mabeckgit/pi-microscope/Drawings/camera_module/OTHER_FORMATS/RspCameraMia/plastic_Smooth_bump.png

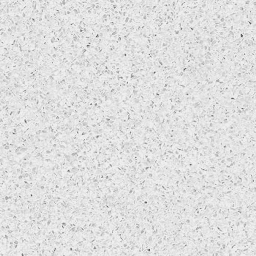
Drawings/camera_module/OTHER_FORMATS/RspCameraMia/plastic_Smooth_bump.png
