mabeckgit/pi-microscope/Drawings/camera_module/RENDERS/PiCamera2back.png

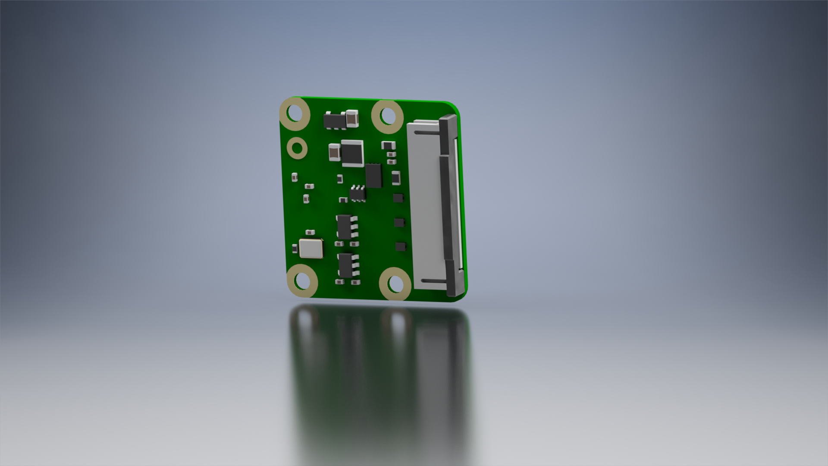
Drawings/camera_module/RENDERS/PiCamera2back.png
