mabeckgit/pi-microscope/Drawings/camera_module/RENDERS/PiCamera2front.png

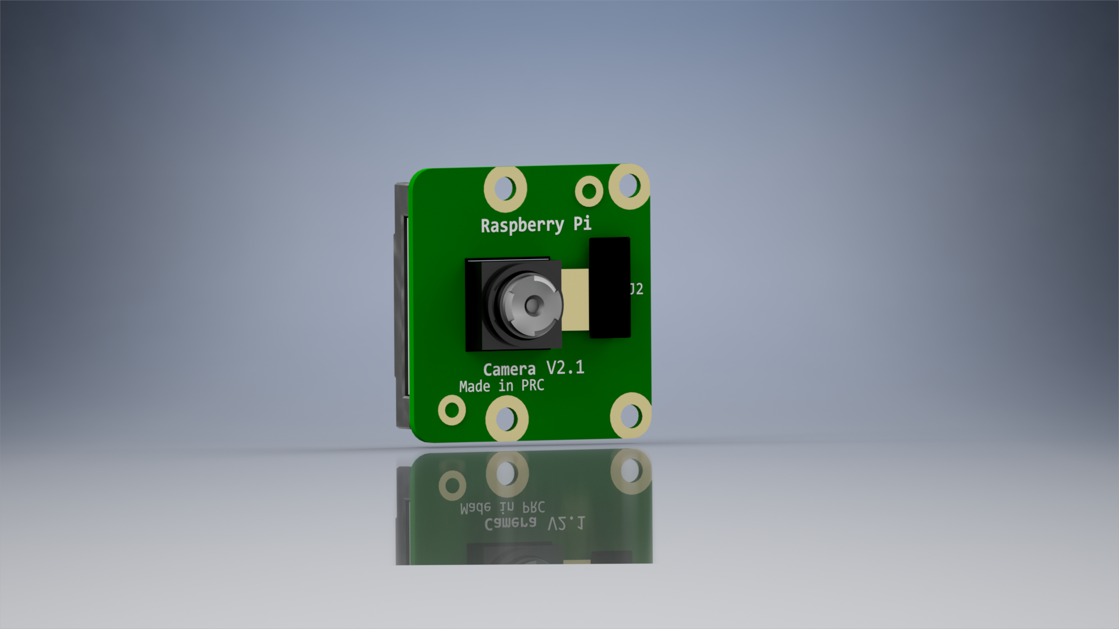
Drawings/camera_module/RENDERS/PiCamera2front.png
