mabeckgit/pi-microscope/Drawings/camera_module/RENDERS/PiCamera2side.png

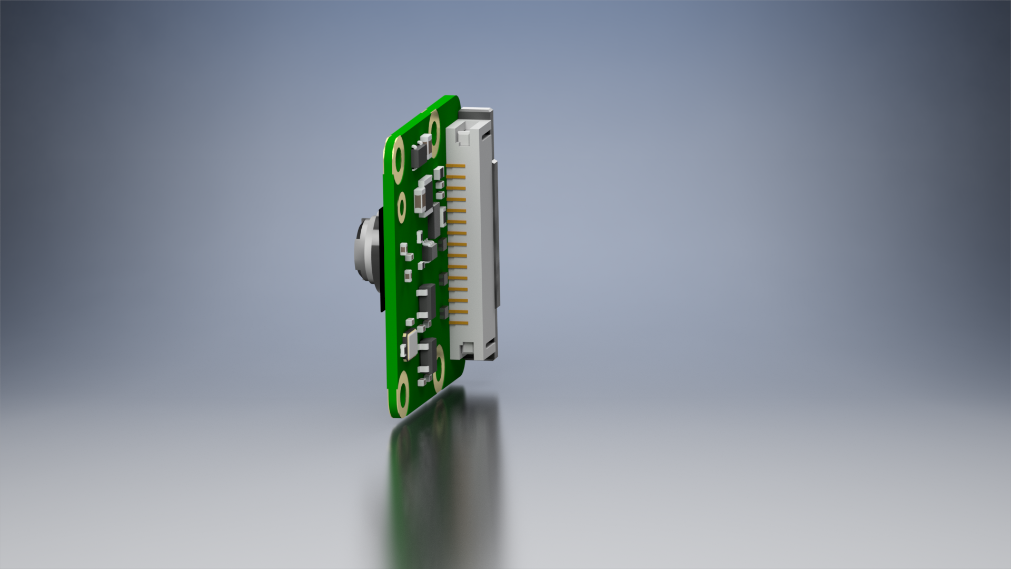
Drawings/camera_module/RENDERS/PiCamera2side.png
