mabeckgit/pi-microscope/Program/1.jpg

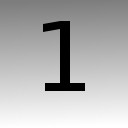
Program/1.jpg
