mabeckgit/pi-microscope/Program/2.jpg

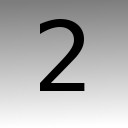
Program/2.jpg
