mabeckgit/pi-microscope/Program/3.jpg

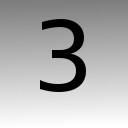
Program/3.jpg
