mabeckgit/pi-microscope/Program/wxGlade-1.0.1/wxGlade-1.0.1/docs/html/_images/Calculator06_P0P0.png

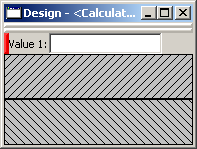
Program/wxGlade-1.0.1/wxGlade-1.0.1/docs/html/_images/Calculator06_P0P0.png
