mabeckgit/pi-microscope/Program/wxGlade-1.0.1/wxGlade-1.0.1/docs/html/_images/Calculator06_P1P0.png

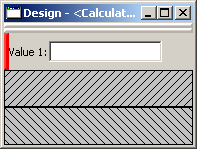
Program/wxGlade-1.0.1/wxGlade-1.0.1/docs/html/_images/Calculator06_P1P0.png
