mabeckgit/pi-microscope/Program/wxGlade-1.0.1/wxGlade-1.0.1/docs/html/_images/Calculator07_Menu_Editor.png

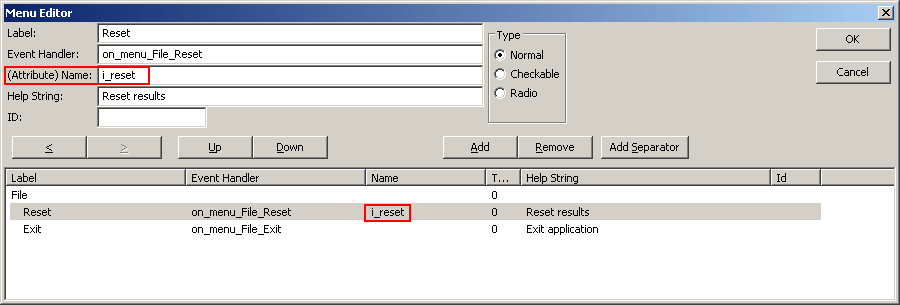
Program/wxGlade-1.0.1/wxGlade-1.0.1/docs/html/_images/Calculator07_Menu_Editor.png
