mabeckgit/pi-microscope/Program/wxGlade-1.0.1/wxGlade-1.0.1/docs/html/_images/Calculator_06_PythonCode.png

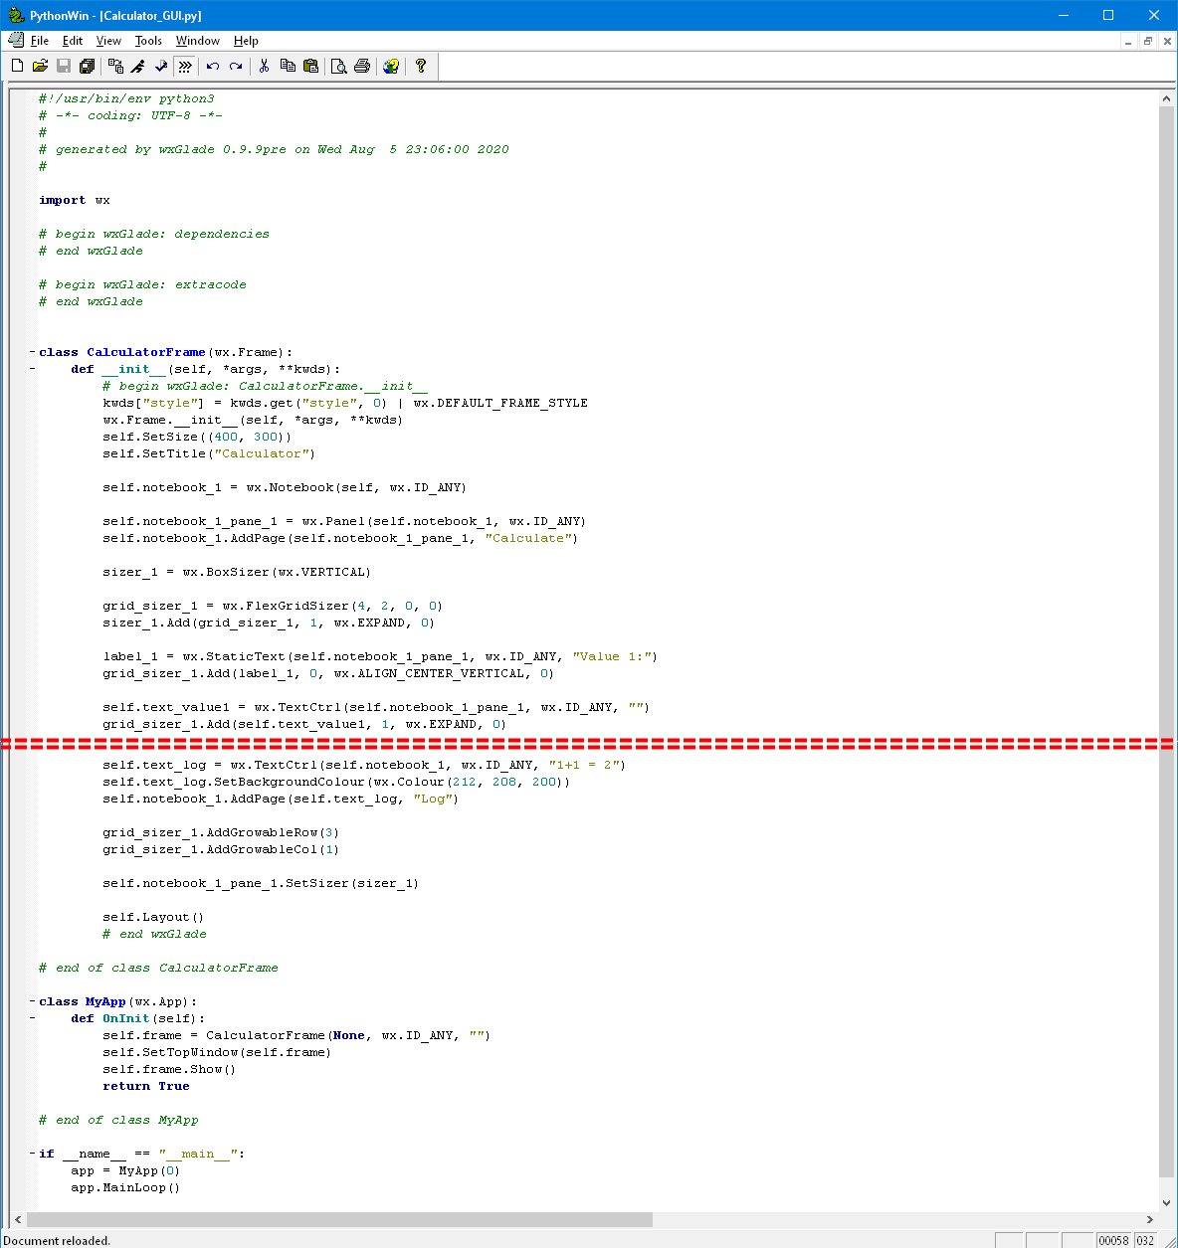
Program/wxGlade-1.0.1/wxGlade-1.0.1/docs/html/_images/Calculator_06_PythonCode.png
