mabeckgit/pi-microscope/Program/wxGlade-1.0.1/wxGlade-1.0.1/docs/html/_images/CalculatorFlexGridSizerDesign.png

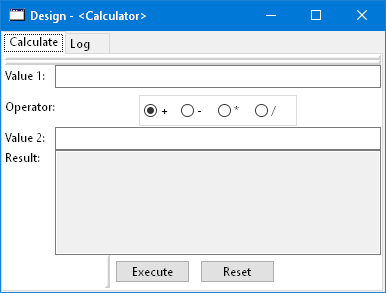
Program/wxGlade-1.0.1/wxGlade-1.0.1/docs/html/_images/CalculatorFlexGridSizerDesign.png
