mabeckgit/pi-microscope/Program/wxGlade-1.0.1/wxGlade-1.0.1/docs/html/_images/NewSizer_CalculatorHorizontal.png

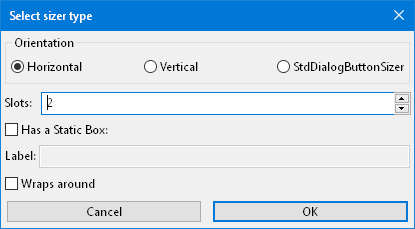
Program/wxGlade-1.0.1/wxGlade-1.0.1/docs/html/_images/NewSizer_CalculatorHorizontal.png
