mabeckgit/pi-microscope/Drawings/cameraholder2.stl

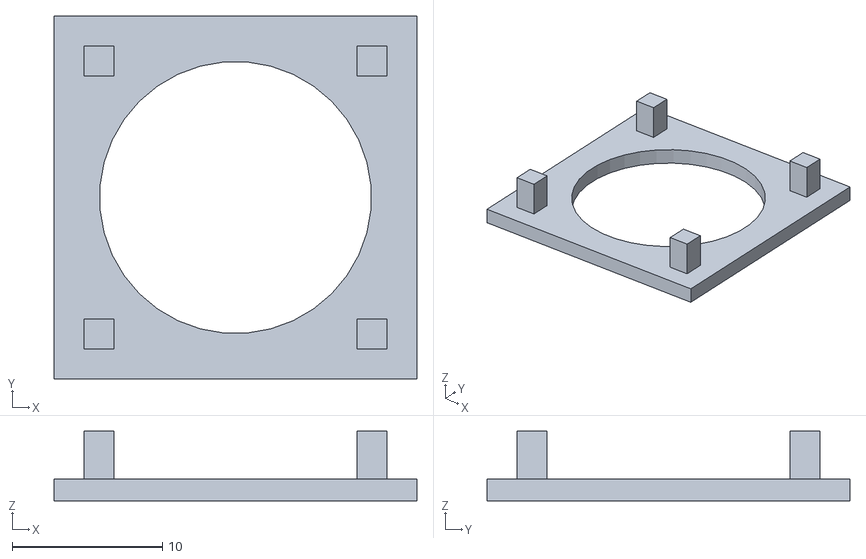
[picture p83: CAD file, 2021-08-16]
Drawings/cameraholder2.stl
24.1 x 24.1 x 4.65
