mabeckgit/pi-microscope/Drawings/Baseplate_Rails.stl

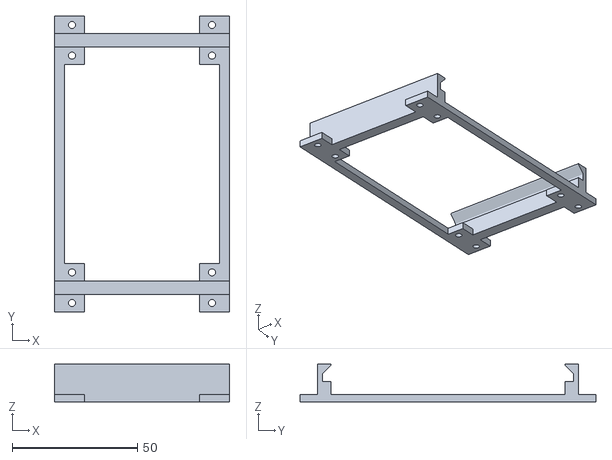
[picture p84: CAD file, 2021-08-16]
Drawings/Baseplate_Rails.stl
70.0 x 118.2 x 15.0
