mabeckgit/pi-microscope/Drawings/Large_Toothed_Rod.stl

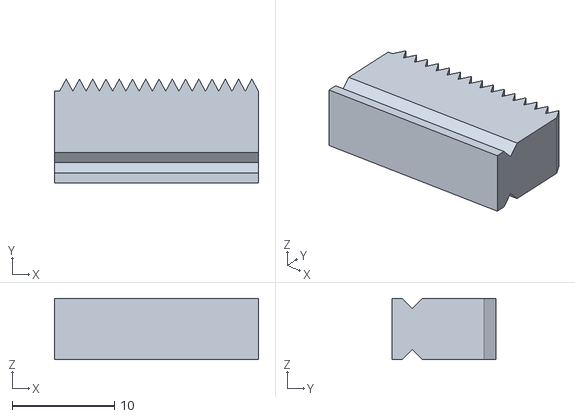
[picture p85: CAD file, 2021-08-16]
Drawings/Large_Toothed_Rod.stl
20.0 x 10.2 x 6.00
