mabeckgit/pi-microscope/Drawings/Camera-Clip.stl

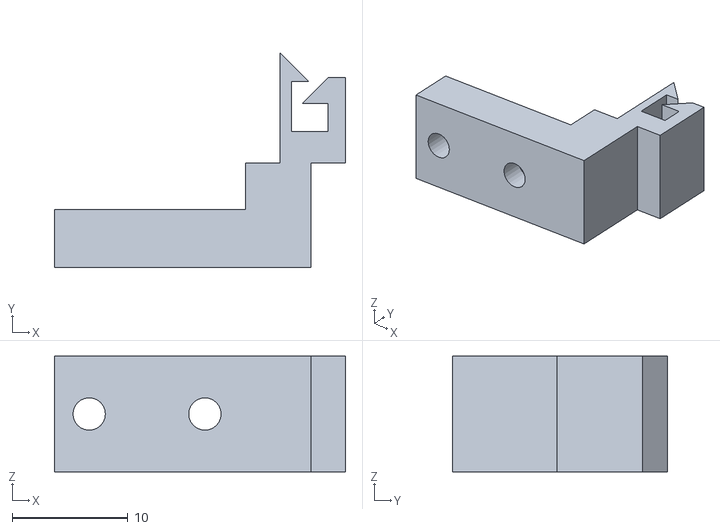
[picture p86: CAD file, 2021-08-16]
Drawings/Camera-Clip.stl
25.2 x 18.6 x 10.00
