mabeckgit/pi-microscope/Drawings/Guidance-Rail-Flat.stl

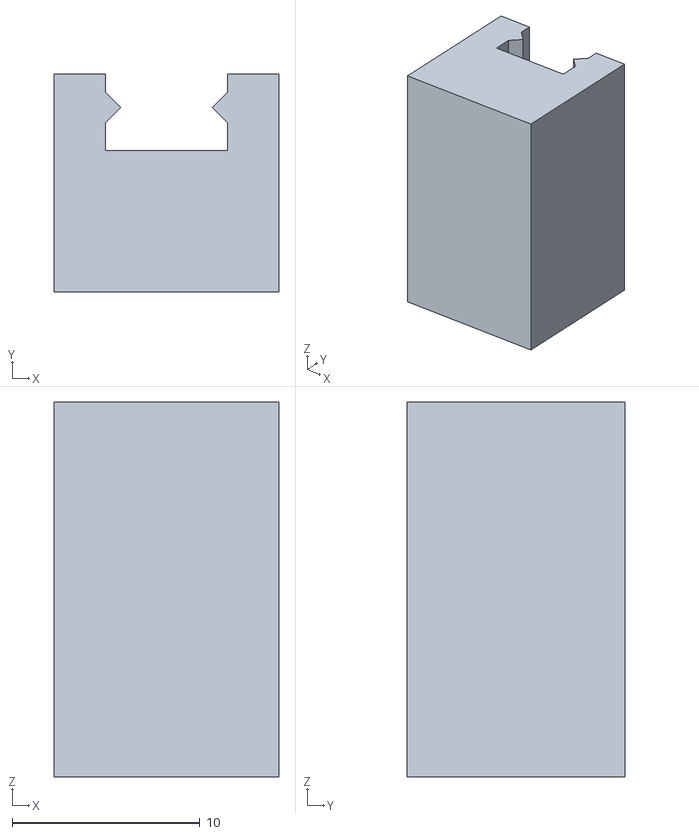
[picture p87: CAD file, 2021-08-16]
Drawings/Guidance-Rail-Flat.stl
12.0 x 11.6 x 20.0
