mabeckgit/pi-microscope/Drawings/Y-Tower-Right.stl

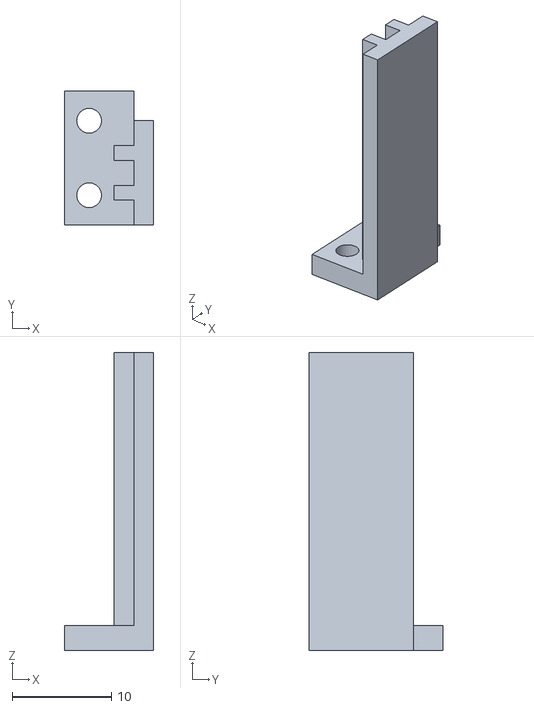
[picture p88: CAD file, 2021-08-16]
Drawings/Y-Tower-Right.stl
9.00 x 13.5 x 30.0
