mabeckgit/pi-microscope/Drawings/Camera-back.stl

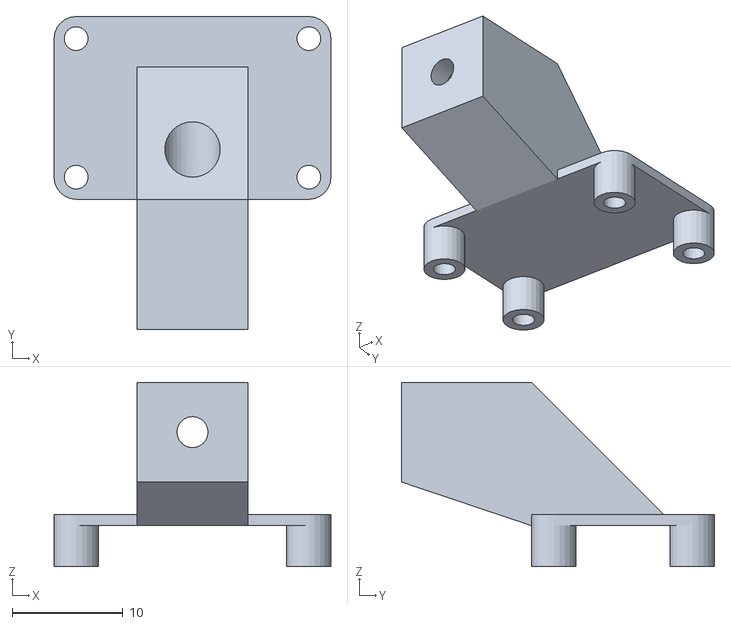
[picture p89: CAD file, 2021-08-16]
Drawings/Camera-back.stl
25.0 x 28.3 x 16.7
